cgrossde/LIR2450-USB-Charger/3D-Model/3D-Model.jpg

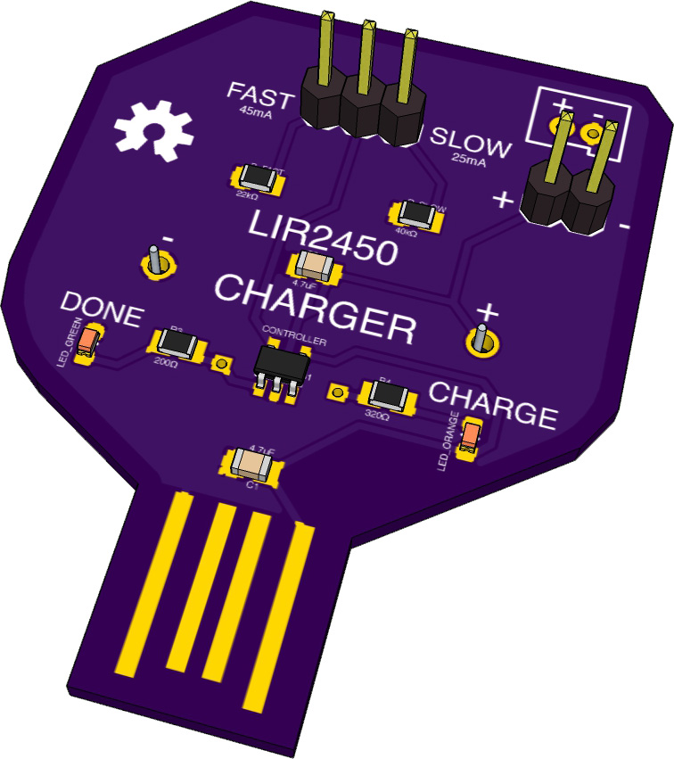
3D-Model/3D-Model.jpg
