cgrossde/LIR2450-USB-Charger/3D-Model/3D-Model/eagleUp_usb_lir2456_charger_top_board.png

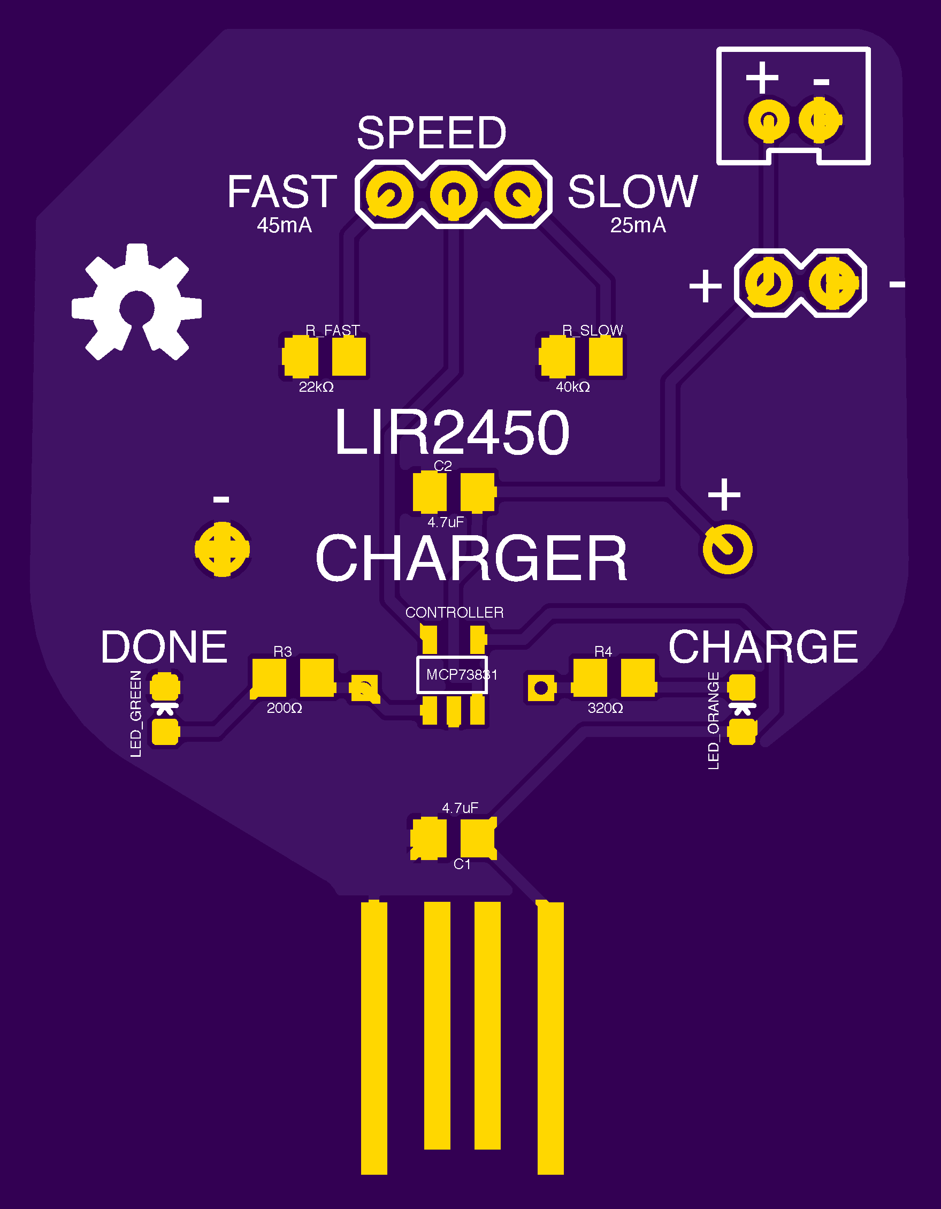
3D-Model/3D-Model/eagleUp_usb_lir2456_charger_top_board.png
