cgrossde/LIR2450-USB-Charger/3D-Model/3D-Model_back.jpg

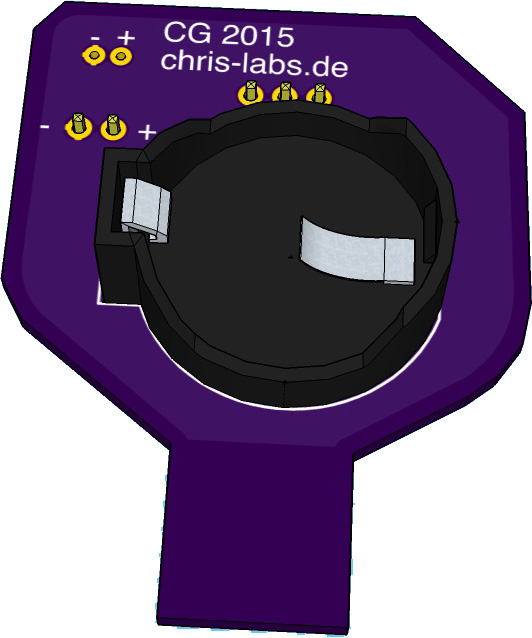
3D-Model/3D-Model_back.jpg
