cgrossde/LIR2450-USB-Charger/PCB-Masks/eagleUp_usb_lir2456_charger_bottom_mask.png

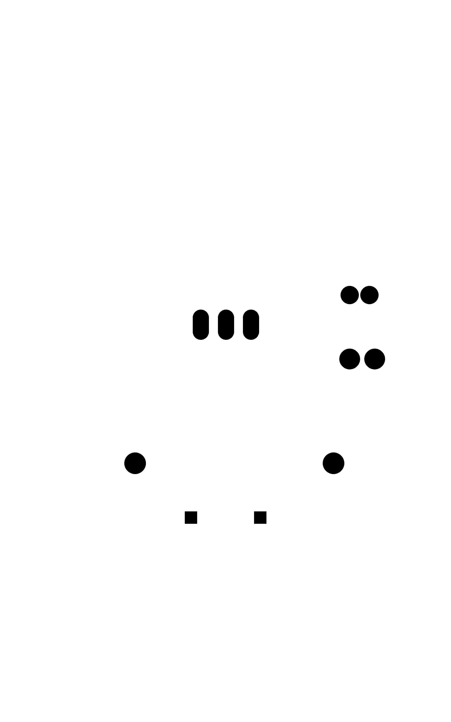
PCB-Masks/eagleUp_usb_lir2456_charger_bottom_mask.png
