cgrossde/LIR2450-USB-Charger/PCB-Masks/eagleUp_usb_lir2456_charger_outline.png

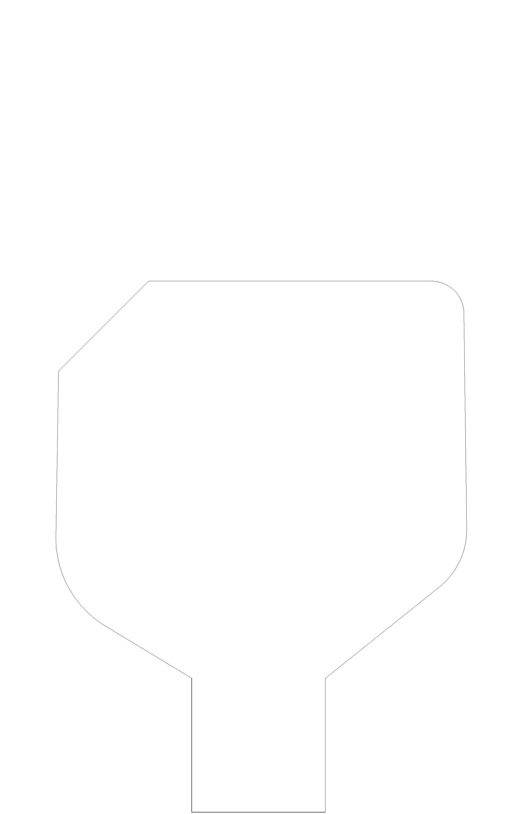
PCB-Masks/eagleUp_usb_lir2456_charger_outline.png
