cgrossde/LIR2450-USB-Charger/3D-Model/3D-Model/material_2.jpg

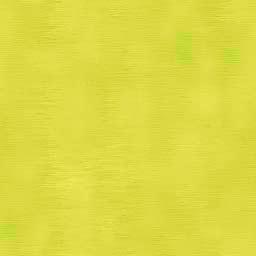
3D-Model/3D-Model/material_2.jpg
